Akash-Harapanahalli/YawYaw/Boards/Central Board board design 1/Central Board board design 1-1.png

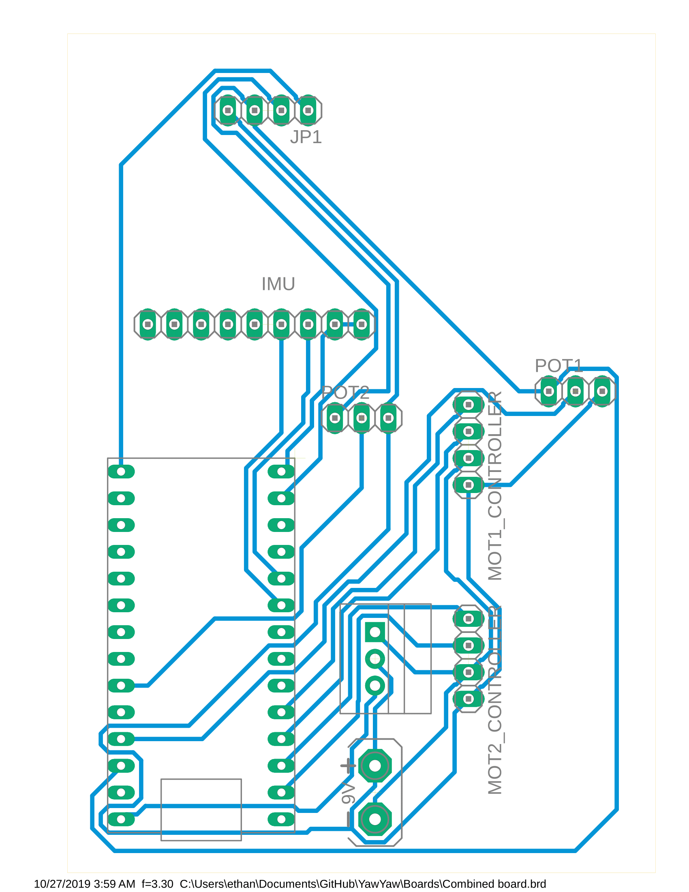
Boards/Central Board board design 1/Central Board board design 1-1.png
