Akash-Harapanahalli/YawYaw/motor_test/MotorDriver.cpp

#ifndef __MOTORDRIVER_CPP__
#define __MOTORDRIVER_CPP__

/**
 * MotorDriver.cpp
 */

#include "MotorDriver.h"
#include <Arduino.h>

/**
 * Sets up the digital out pins and the PID if specified.
 */
void MotorDriver::setup(int _in1, int _in2){
    this->in1 = _in1;
    this->in2 = _in2;
    pinMode(_in1, OUTPUT);
    pinMode(_in2, OUTPUT);
}
void MotorDriver::setup(int _in1, int _in2, float _kP, float _kI, float _kD, int _dt){
    this->in1 = _in1;
    this->in2 = _in2;
    pinMode(_in1, OUTPUT);
    pinMode(_in2, OUTPUT);
    this->pid.setConstants(_kP, _kI, _kD, _dt);
}

/**
 * Power is taken in the range from -255 to 255 (dual 8-bit)
 * Powering the motors is based on a potential difference between the in1 and in2 leads on the driver.
 * When in1 is LOW, the motor is powered "forward" and when in2 is LOW, the motor is powered "backward".
 */
void MotorDriver::setPower(int power){
    if(power > 0){
        digitalWrite(this->in1, LOW);
        analogWrite(this->in2, power);
    } else if(power < 0){
        analogWrite(this->in1, power);
        digitalWrite(this->in2, LOW);
    } else {
        digitalWrite(this->in1, LOW);
        digitalWrite(this->in2, LOW);
    }
}

/**
 * Steps the internal PID and powers the motor.
 */
void MotorDriver::step(float error){
    this->setPower(this->pid.step(error));
}

#endif
